mckacz/sensors/firmware/sensors/vcc.cpp

/*
  Vcc - A supply voltage measuring library for Arduino

  Created by Ivo Pullens, Emmission, 2014
  
  Inspired by:
  http://provideyourown.com/2012/secret-arduino-voltmeter-measure-battery-voltage/
  
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
  You should have received a copy of the GNU Lesser General Public
  License along with this library; if not, write to the Free Software
  Foundation, Inc., 51 Franklin St, Fifth Floor, Boston, MA  02110-1301  USA
*/

#include "vcc.h"

Vcc::Vcc( const float correction )
  : m_correction(correction)
{
}

#if defined(__AVR_ATmega32U4__) || defined(__AVR_ATmega1280__) || defined(__AVR_ATmega2560__)
#define ADMUX_VCCWRT1V1 (_BV(REFS0) | _BV(MUX4) | _BV(MUX3) | _BV(MUX2) | _BV(MUX1))
#elif defined (__AVR_ATtiny24__) || defined(__AVR_ATtiny44__) || defined(__AVR_ATtiny84__)
#define ADMUX_VCCWRT1V1 (_BV(MUX5) | _BV(MUX0))
#elif defined (__AVR_ATtiny25__) || defined(__AVR_ATtiny45__) || defined(__AVR_ATtiny85__)
#define ADMUX_VCCWRT1V1 (_BV(MUX3) | _BV(MUX2))
#else
#define ADMUX_VCCWRT1V1 (_BV(REFS0) | _BV(MUX3) | _BV(MUX2) | _BV(MUX1))
#endif  

float Vcc::Read_Volts(void)
{
  // Calculate Vcc (in V)
  float vcc = 1.1*1024.0 / Read_ADC();

  // Apply compensation
  vcc *= m_correction;

  return vcc;
}

uint16_t Vcc::Read_ADC(void)
{
  // Read 1.1V reference against AVcc
  // set the reference to Vcc and the measurement to the internal 1.1V reference
  if (ADMUX != ADMUX_VCCWRT1V1)
  {
    ADMUX = ADMUX_VCCWRT1V1;

    // Bandgap reference start-up time: max 70us
    // Wait for Vref to settle.
    delayMicroseconds(350);
  }

  // Start conversion and wait for it to finish.
  ADCSRA |= _BV(ADSC);
  while (bit_is_set(ADCSRA,ADSC)) {};

  return ADC;
}

float Vcc::Read_Perc(const float range_min, const float range_max, const boolean clip)
{
  // Read Vcc and convert to percentage
  float perc = 100.0 * (Read_Volts()-range_min) / (range_max-range_min);
  // Clip to [0..100]% range, when requested.
  if (clip)
    perc = constrain(perc, 0.0, 100.0);

  return perc;
}
